Benny-Gil/Lazarack/reference-images/photo-2.jpeg

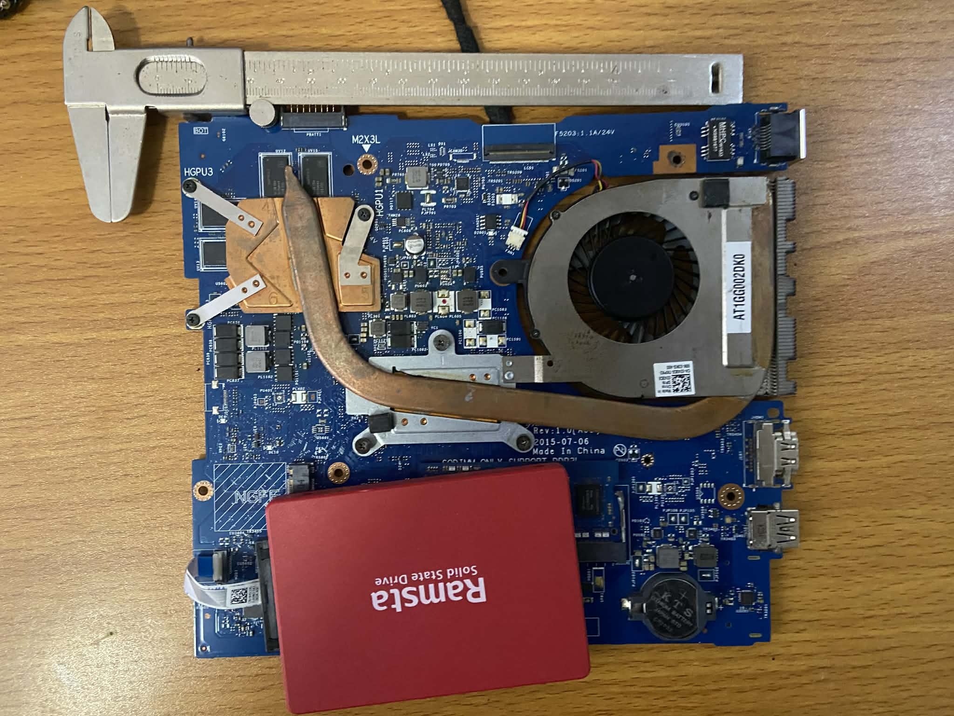
reference-images/photo-2.jpeg
